evilwombat/stm-bmc/photos/analog_section.jpg

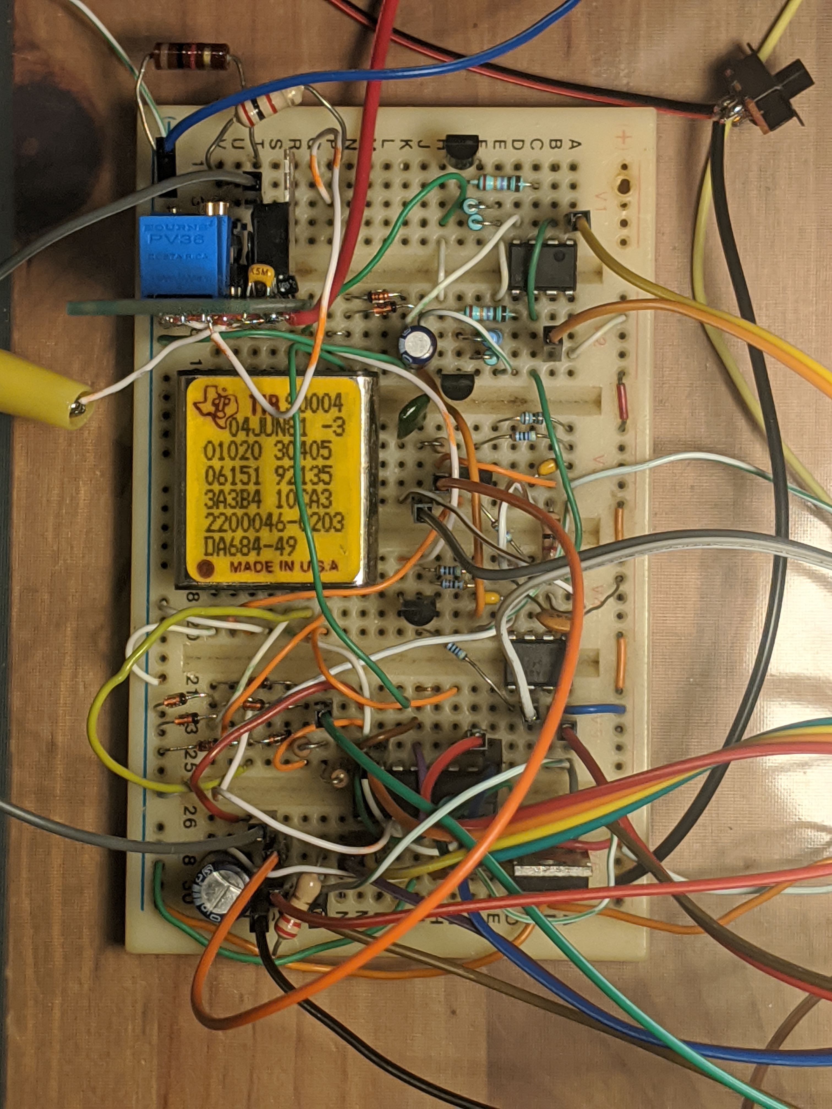
photos/analog_section.jpg
