evilwombat/stm-bmc/photos/analog_section_2.jpg

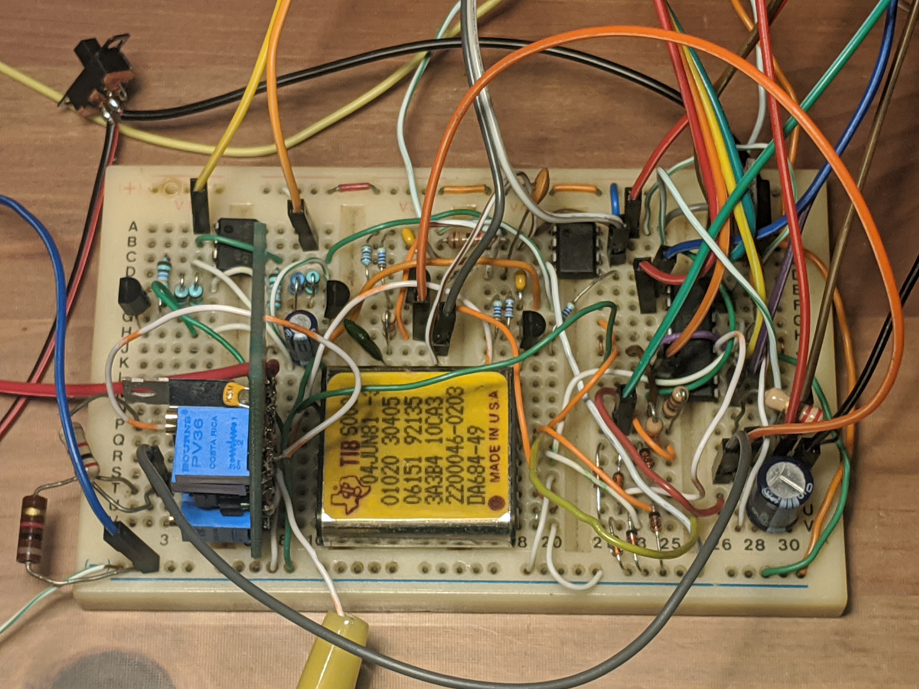
photos/analog_section_2.jpg
