evilwombat/stm-bmc/Src/payload.h

#include <stdint.h>
const char payload_raw[] = {
	0x3f, 0xfa, 0x60, 0x74, 0xac, 0xb1, 0xbe, 0xb4, 0xba, 0xff, 0xff, 0xff, 0xff, 0xff, 0x6a, 0xc2, 0xff, 0x0f, 0x2b, 0x05, 
	0x8f, 0xb8, 0xff, 0xff, 0xff, 0xdc, 0xef, 0x4a, 0xe5, 0xb9, 0xfe, 0xdb, 0xbf, 0x05, 0xfd, 0x0e, 0x36, 0xf8, 0xbd, 0x40, 
	0x3d, 0x0e, 0xf8, 0xfe, 0xfb, 0x05, 0xfe, 0x0e, 0xf4, 0xbc, 0xfd, 0x0e, 0xfe, 0xfd, 0xb7, 0x40, 0x24, 0x4d, 0xf7, 0xd5, 
	0x0f, 0x2e, 0xe7, 0xb9, 0xef, 0x42, 0xff, 0xff, 0x00, 0xdd, 0xf5, 0xb4, 0xa5, 0x9e, 0xb0, 0x0b, 0xff, 0xad, 0xe7, 0x9e, 
	0xfc, 0x0a, 0xff, 0x9c, 0xe5, 0x9e, 0xb7, 0xdd, 0xff, 0x40, 0xfe, 0xc5, 0x03, 0x2e, 0xb0, 0x0f, 0xff, 0xad, 0xe5, 0x9e, 
	0xb7, 0xdc, 0xff, 0x40, 0xfe, 0xc4, 0x03, 0x2e, 0x8f, 0xb8, 0xff, 0x40, 0xff, 0xf7, 0xfe, 0xbf, 0xb0, 0x0b, 0x7f, 0xcd, 
	0xf9, 0xb4, 0xbf, 0x0f, 0x47, 0xff, 0xe5, 0x9e, 0xb0, 0x0f, 0xff, 0xbd, 0x3c, 0x07, 0xef, 0xdb, 0xb0, 0x0f, 0x7f, 0xbd, 
	0x3c, 0x07, 0xef, 0xdb, 0x00, 0x08, 0x27, 0x40, 0xff, 0xf3, 0xfe, 0xbf, 0xd2, 0x16, 0x08, 0xb0, 0x20, 0x07, 0x53, 0x7f, 
	0xff, 0xda, 0xf8, 0xd8, 0xb9, 0xb9, 0x20, 0x07, 0x57, 0x6f, 0xa0, 0x05, 0x78, 0x05, 0xaf, 0xb9, 0x00, 0x08, 0x1f, 0x00, 
	0xb0, 0x0b, 0x7f, 0xcc, 0x36, 0x07, 0xef, 0xcf, 0xb0, 0x0b, 0xff, 0xbc, 0x37, 0x07, 0xef, 0xcf, 0xb0, 0x0f, 0x7f, 0xbc, 
	0xbf, 0xdf, 0x37, 0x07, 0xef, 0xcf, 0x00, 0x08, 0x46, 0x00, 0xb0, 0x0b, 0x7f, 0xbb, 0xbf, 0xdd, 0x20, 0x07, 0x93, 0x4f, 
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
	0xfc, 0xed, 0xfc, 0x14, 0xbd, 0xec, 0x3d, 0xe7, 0x3c, 0xa3, 0xff, 0xd4, 0x0c, 0x2e, 0xbf, 0xdc, 0xec, 0x8f, 0x8f, 0xb8, 
	0xff, 0xf7, 0xff, 0xbf, 0xef, 0x4a, 0xb0, 0x0b, 0xff, 0x8d, 0xff, 0xde, 0xfb, 0xb9, 0x00, 0x08, 0xe4, 0x00, 0xff, 0xdc, 
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
};
