evilwombat/stm-bmc/Src/morning_music.h

#pragma once
#include <stdint.h>

struct note {
    uint16_t start_time;
    uint8_t duration;
    uint8_t note;
};

const struct note right_hand[] = {
    {0,  16, 62},
    {16,  8, 67},
    {24,  8, 69},
    {32,  8, 71},
    {40,  8, 67},
    {48,  24, 72},
    {72,  4, 71},
    {76,  4, 69},
    {80,  8, 71},
    {88,  8, 67},
    {96,  8, 64},
    {104,  8, 69},
    {112,  2, 66},
    {114,  2, 67},
    {116,  2, 66},
    {118,  2, 67},
    {120,  2, 66},
    {122,  2, 67},
    {124,  4, 64},
    {128,  16, 62},
    {144,  8, 67},
    {152,  8, 69},
    {160,  8, 71},
    {168,  8, 67},
    {176,  24, 72},
    {200,  8, 69},
    {208,  8, 71},
    {216,  8, 72},
    {224,  12, 69},
    {236,  4, 67},
    {240,  16, 67},
    {256,  8, 67},
    {264,  8, 66},
    {272,  8, 64},
    {280,  8, 71},
    {288,  8, 64},
    {296,  8, 67},
    {304,  24, 60},
    {328,  4, 62},
    {332,  4, 64},
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
};

const struct note left_hand[] = {
    {16,  16, 59},
    {32,  16, 55},
    {48,  16, 57},
    {64,  16, 54},
    {80,  16, 55},
    {96,  16, 52},
    {112,  8, 50},
    {120,  8, 52},
    {128,  8, 54},
    {136,  8, 50},
    {144,  16, 55},
    {160,  24, 52},
    {184,  4, 52},
    {188,  4, 50},
    {192,  8, 52},
    {200,  8, 48},
    {208,  8, 50},
    {216,  8, 52},
    {224,  8, 54},
    {232,  8, 50},
    {240,  16, 55},
    {256,  8, 55},
    {264,  8, 54},
    {272,  16, 52},
    {288,  16, 55},
    {304,  16, 57},
    {320,  8, 45},
    {336,  16, 50},
    {352,  16, 54},
    {368,  16, 55},
    {384,  8, 43},
    {400,  16, 48},
    {416,  16, 52},
    {432,  8, 45},
    {440,  8, 47},
    {448,  8, 48},
    {456,  8, 45},
    {464,  8, 50},
    {472,  16, 50},
    {488,  8, 50},
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
};
const uint16_t note_values[] = {
    65535,
    65535,
    65535,
    65535,
    65535,
    65535,
    65535,
    65535,
    65535,
    65535,
    65535,
    64792,
    61156,
    57723,
    54483,
    51425,
    48539,
    45815,
    43243,
    40816,
    38525,
    36363,
    34322,
    32396,
    30578,
    28861,
    27241,
    25712,
    24269,
    22907,
    21621,
    20408,
    19262,
    18181,
    17161,
    16198,
    15289,
    14430,
    13620,
    12856,
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
};
