evilwombat/stm-bmc/Src/loader.c

#include <string.h>
#include "main.h"
#include "bmc.h"
#include "gfx_util.h"
#include "util.h"
#include "console.h"
#include "block_io.h"
#include "music.h"
#include "loader.h"
#include "payload.h"

extern TIM_HandleTypeDef htim3;
extern TIM_HandleTypeDef htim4;

struct payload_header {
    uint16_t size;
    uint16_t body_crc;
    uint8_t name[10];
    uint16_t header_crc;
} __attribute__((packed));

#define PAYLOAD_MAX_SIZE    4096

/* Placed at a fixed address using linker script. This way payloads can avoid being position-independent. */
uint8_t __attribute__((section (".payloadBufferSection"))) payload_buf[PAYLOAD_MAX_SIZE];

void write_payload()
{
    int i, error_count = 0;
    int payload_size = sizeof(payload_raw);
    int num_blocks = (payload_size + BLOCK_LEN - 1) / BLOCK_LEN;

    memset(payload_buf, 0, sizeof(payload_buf));

    /* Unscramble the payload. To make absolutely sure that we're launching a payload that was
     * loaded from the bubble device (rather than our own baked-in copy) we store the baked-in
     * payload in bit-flipped form, to rule out the possibility of inadvertently jumping to it
     * in flash and seeing a valid result.
     */
    for (i = 0; i < sizeof(payload_raw); i++)
        payload_buf[i] = payload_raw[i] ^ 0xff;

    con_printf("Writing %d blocks\n", num_blocks);

    for (i = 0; i < num_blocks; i++) {
        con_printf("Erasing %03d\r", i);
        block_erase(i);

        con_printf("Writing %03d\r", i);

        if (block_write(i, payload_buf + i * BLOCK_LEN) != 0) {
            con_printf("That failed??\n");
            error_count++;
        }
    }

    con_printf("\n");

    if (error_count == 0) {
        con_printf("Payload written\n");
    } else {
        con_printf("Encountered %d errors\n", error_count);
    }
    bmc_idle();
    wait_for_drive_disarm();
}

int load_payload()
{
    int num_blocks = 0;
    int i, ret, error_count = 0;
    uint16_t body_crc;
    struct payload_header hdr;

    bmc_idle();
    memset(&hdr, 0, sizeof(hdr));
    memset(payload_buf, 0, sizeof(payload_buf));

    con_printf("Reading header...");

    ret = block_read(0, (uint8_t*)&hdr, &error_count);
    if (ret)  {
        con_printf("\nHeader read failed\n");
        bmc_shut_down();
    }

    if (crc16((uint8_t*)&hdr, sizeof(hdr) - 2) != hdr.header_crc) {
        con_printf("\nHeader CRC is valid\n");
        dump_buffer((uint8_t*) &hdr, sizeof(hdr));
        bmc_shut_down();
    }

    con_printf(" OK!\n");
    con_printf("Loading \"%s\"\n", hdr.name);
    con_printf("Size: %d bytes\n", hdr.size);

    num_blocks = (hdr.size + BLOCK_LEN - 1) / BLOCK_LEN;

    con_printf("Reading payload\n");

    for (i = 0; i < num_blocks; i++) {
        con_printf("Reading block %d/%d\r", i + 1, num_blocks);
        ret = block_read(i + 1, payload_buf + i * BLOCK_LEN, &error_count);

        if (ret != 0) {
            music_stop();
            con_printf("\nThat failed.\n");
            uart_printf("Unrecoverable error reading block %d\n", i);
            bmc_shut_down();
        }
    }

    con_printf("\n");
    con_printf("Errors fixed: %d\n", error_count);

    body_crc = crc16(payload_buf, hdr.size);

    con_printf("CRC is %04X ", body_crc);

    if (hdr.body_crc == body_crc) {
        con_printf("- OK!\n");
        con_printf("Loading complete\n");
        ret = 0;
    } else {
        con_printf("- FAIL!\n");
        con_printf("Loading complete???\n");
        ret = -1;
    }

    bmc_idle();
    return ret;
}

void launch_payload()
{
    volatile uint32_t branch_destination = (uint32_t) payload_buf;
    int i;

    wait_for_drive_disarm();

    con_printf("Launching payload\n");

    __enable_irq();
    for (i = 3; i >= 0; i--) {
        con_printf("\rin %d...", i);
        HAL_Delay(1000);
    }

    con_printf("\nJumping to payload\n");

    __disable_irq();

    branch_destination |= 1;    /* Thumb */

    HAL_TIM_OC_Stop(&htim3, TIM_CHANNEL_4);
    HAL_TIM_OC_Stop(&htim4, TIM_CHANNEL_4);

    __HAL_TIM_ENABLE(&htim3);
    __HAL_TIM_ENABLE(&htim4);

    /* Leave TIM4 running, as a pseudo-RNG for games, so that payloads don't need to pull in the
     * entire timer HAL
     */
    TIM4->CNT = 0;
    TIM4->CR1 &= ~TIM_CR1_CEN;
    TIM4->ARR = 512;
    TIM4->CCR4 = 0;
    TIM4->CNT = 0;
    TIM4->CR1 |= TIM_CR1_CEN;

    asm volatile("blx %[dest]"
           : /* No result */
           : [dest]"r"   (branch_destination) /* Place to jump */
           : /* No clobbers */
    );

    /* We should not get here, unless the payload 'returns' via LR */

    con_printf("We're BACK??\n");

    uart_printf("We're BACK??\n");

}
