evilwombat/stm-bmc/Src/gfx_util.c

#include "main.h"
#include "gfx_util.h"
#include "lcd.h"
#include "util.h"
#include "encoder.h"
#include "console.h"

/* Bitmaps of the big digits for the warmup countdown */

const static uint8_t digit_data[10 * 7] = {
    /* 0 */
    0b1111111,
    0b1000011,
    0b1000101,
    0b1001001,
    0b1010001,
    0b1100001,
    0b1111111,

    /* 1 */
    0b0001000,
    0b0011000,
    0b0001000,
    0b0001000,
    0b0001000,
    0b0001000,
    0b0001000,


    /* 2 */
    0b1111111,
    0b1000001,
    0b0000001,
    0b1111111,
    0b1000000,
    0b1000000,
    0b1111111,

    /* 3 */
    0b1111111,
    0b1000001,
    0b0000001,
    0b0011111,
    0b0000001,
    0b1000001,
    0b1111111,

    /* 4 */
    0b1000000,
    0b1000000,
    0b1000100,
    0b1000100,
    0b1111111,
    0b0000100,
    0b0000100,


    /* 5 */
    0b1111111,
    0b1000000,
    0b1000000,
    0b1111111,
    0b0000001,
    0b1000001,
    0b1111111,

    /* 6 */
    0b1111111,
    0b1000000,
    0b1000000,
    0b1111111,
    0b1000001,
    0b1000001,
    0b1111111,

    /* 7 */
    0b1111111,
    0b0000001,
    0b0000001,
    0b0000010,
    0b0000100,
    0b0001000,
    0b0010000,

    /* 8 */
    0b1111111,
    0b1000001,
    0b1000001,
    0b1111111,
    0b1000001,
    0b1000001,
    0b1111111,

    /* 9 */
    0b1111111,
    0b1000001,
    0b1000001,
    0b1111111,
    0b0000001,
    0b0000001,
    0b1111111,
};

static void fill_block(int x, int y, int scale, int shadow)
{
    int i, j;

    for (i = 0; i < scale; i++) {
        for (j = 0; j < scale; j++) {
            if (!shadow || (((x + i) ^ (y + j)) & 1))
                    lcd_pset(x + i, y + j, 1);
        }
    }
}

static void clear_block(int x, int y, int scale)
{
    int i, j;

    for (i = 0; i < scale; i++) {
        for (j = 0; j < scale; j++) {
            lcd_pset(x + i, y + j, 0);
        }
    }
}

void gfx_draw_big_digit(int x, int y, int scale, int digit)
{
    int i, j;
    int offset = digit * 7;

    for (i = 0; i < 8; i++)
        for (j = 0; j < 8; j++)
            clear_block(x + i * scale, y + j * scale, scale);

    for (i = 0; i < 7; i++) {
        for (j = 0; j < 7; j++) {
            if (digit_data[offset + j] & BIT(6 - i)) {
                fill_block(x + i * scale, y + j * scale, scale, 0);
                fill_block(x + (i + 1) * scale, y + (j + 1) * scale, scale, 1);
            }
        }
    }
}

void gfx_draw_countdown(int value)
{
    int scale = 4;
    int y = (LCD_HEIGHT - (scale * 8)) / 2;
    int x = (LCD_WIDTH - (scale * 17)) / 2;

    gfx_draw_big_digit(x, y, scale, (value / 10) % 10);
    gfx_draw_big_digit(x + scale * 9, y, scale, value % 10);
}

static void menu_invert_item(int y, int item, int item_height)
{
    lcd_invert_block(0, y + item * item_height - 1, LCD_WIDTH, item_height);
}

int run_menu(const char **items, int y)
{
    uint16_t enc = encoder_read();
    uint16_t last_enc = enc;
    int item_height = con_font_height() + 2;
    int num_items = 0;
    int cur_item = 0;
    int i;

    y++;    /* Make room for upper hilight row */

    while(items[num_items]) {
        con_gotoxy(1, y + num_items * item_height);
        con_printf(items[num_items]);
        con_printf("\n");
        num_items++;
    }

    menu_invert_item(y, cur_item, item_height);
    lcd_update();

    while(1) {

        enc = encoder_read();
        
        if (enc > last_enc) {
            menu_invert_item(y, cur_item, item_height);
            cur_item--;
            if (cur_item < 0)
                cur_item = num_items - 1;
            menu_invert_item(y, cur_item, item_height);
            lcd_update();
        }

        if (enc < last_enc) {
            menu_invert_item(y, cur_item, item_height);
            cur_item++;
            if (cur_item >= num_items)
                cur_item = 0;
            menu_invert_item(y, cur_item, item_height);
            lcd_update();
        }

        last_enc = enc;

        if (encoder_pressed_debounce()) {
            for (i = 0; i < 4; i++) {
                menu_invert_item(y, cur_item, item_height);
                lcd_update();
                HAL_Delay(50);
            }
            while(encoder_pressed_debounce());
            return cur_item;
        }
    }

}
